rhodyboland/ACM/Hardware/Images/IMG_4668.jpg

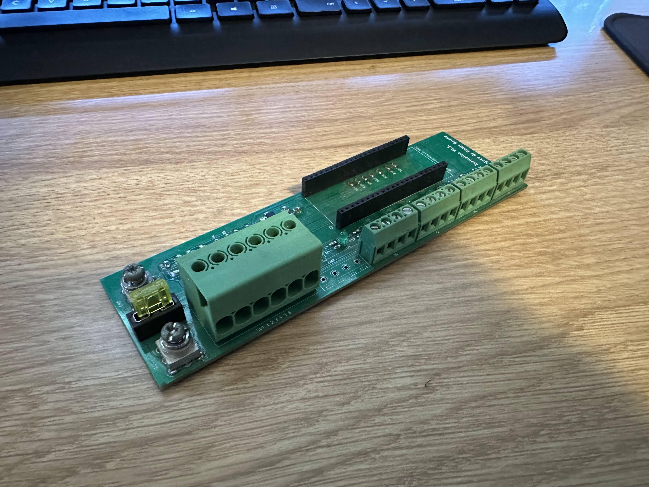
Hardware/Images/IMG_4668.jpg
