rhodyboland/ACM/Hardware/Images/IMG_4669.jpg

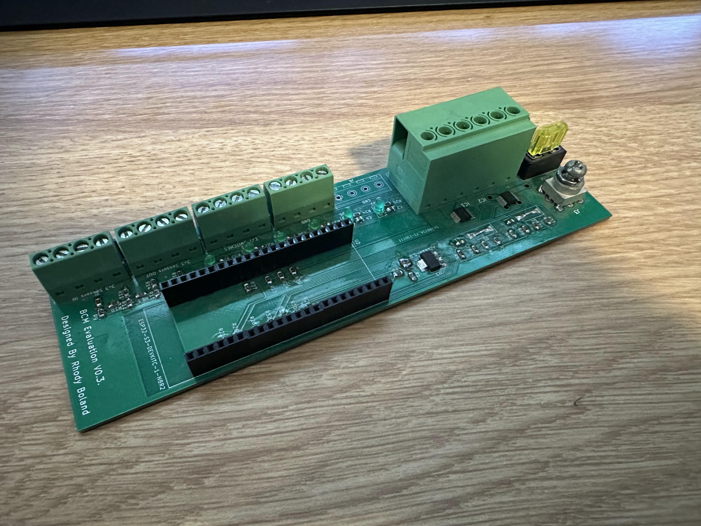
Hardware/Images/IMG_4669.jpg
